kelv1n9/eHack/src/signal_data.h

// TVs
const uint16_t irCommandsTV[] PROGMEM = {
    // {protocol, address, command}
    24, 0x0001, 0x0015,
    24, 0x0010, 0x0015,
    8, 0x007B, 0x0000, 
    8, 0x011C, 0x0012, 
    24, 0x0001, 0x002F,
    24, 0x0001, 0x002E,
    8, 0x0008, 0x0005,
    10, 0xDF00, 0x001C,
    20, 0x000E, 0x000C,
    18, 0x0000, 0x000C,
    20, 0x0007, 0x0002,
    20, 0x0007, 0x00E6,
    8, 0x0050, 0x0017,
    8, 0x0040, 0x0012,
    10, 0x4931, 0x0063,
    8, 0x00AA, 0x001C,
    8, 0x0038, 0x001C,
    10, 0x7A83, 0x0008,
    8, 0x0053, 0x0017,
    10, 0x1818, 0x00C0,
    8, 0x0038, 0x0010,
    8, 0x00AA, 0x00C5,
    8, 0x0004, 0x0008,
    8, 0x0018, 0x0008,
    8, 0x0071, 0x0008,
    10, 0x6F80, 0x000A,
    8, 0x0048, 0x0000,
    10, 0x7B80, 0x0013,
    10, 0x7E80, 0x0018,
    8, 0x0050, 0x0008,
    10, 0x7580, 0x000A,
    10, 0x5780, 0x000A,
    20, 0x000B, 0x000A,
    8, 0x00AA, 0x001B,
    10, 0x4685, 0x0012,
    20, 0x0005, 0x0002,
    20, 0x0008, 0x000F,
    8, 0x0000, 0x0001,
    12, 0x0280, 0x03D0,
    17, 0x0000, 0x000C,
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
};

// Projectors
const uint16_t irCommandsPR[] PROGMEM = {
    // {protocol, address, command}
    20, 0x0007, 0x00E6,
    24, 0x0054, 0x0015,
    8, 0x0000, 0x008A,
    10, 0x5583, 0x6F90,
    10, 0x0381, 0x0FF0,
    10, 0x4587, 0xE817,
    8, 0x0008, 0x000B,
    10, 0x1308, 0x7887,
    8, 0x0002, 0x001D,
    10, 0xF483, 0xB04F,
    10, 0x1980, 0xEF10,
    8, 0x0080, 0x0051,
    10, 0x4040, 0xF50A,
    10, 0x3000, 0xB14E,
    10, 0x3000, 0xB04F,
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
        113, 114, 115, 116, 117, 118, 119, 120, 121, 122, 123, 124
    }; // All Channels
const uint8_t noiseAddress[][2] = {{0x55, 0x55}, {0xAA, 0xAA}, {0xA0, 0xAA}, {0xAB, 0xAA}, {0xAC, 0xAA}, {0xAD, 0xAA}};

const uint8_t bManCode[6] = {0x48,0xa9,0xca,0xe6,0xd8,0xc2};
